UofGlasgow-ES-Team5/Centralized-Hazard-Detection-System-/Images/Schematic_Diagrams/KiCad Schematic Files/CentralNode.kicad_sch

## KiCad design Images/Schematic_Diagrams/KiCad Schematic Files/CentralNode.kicad_sch (2024-04-15)

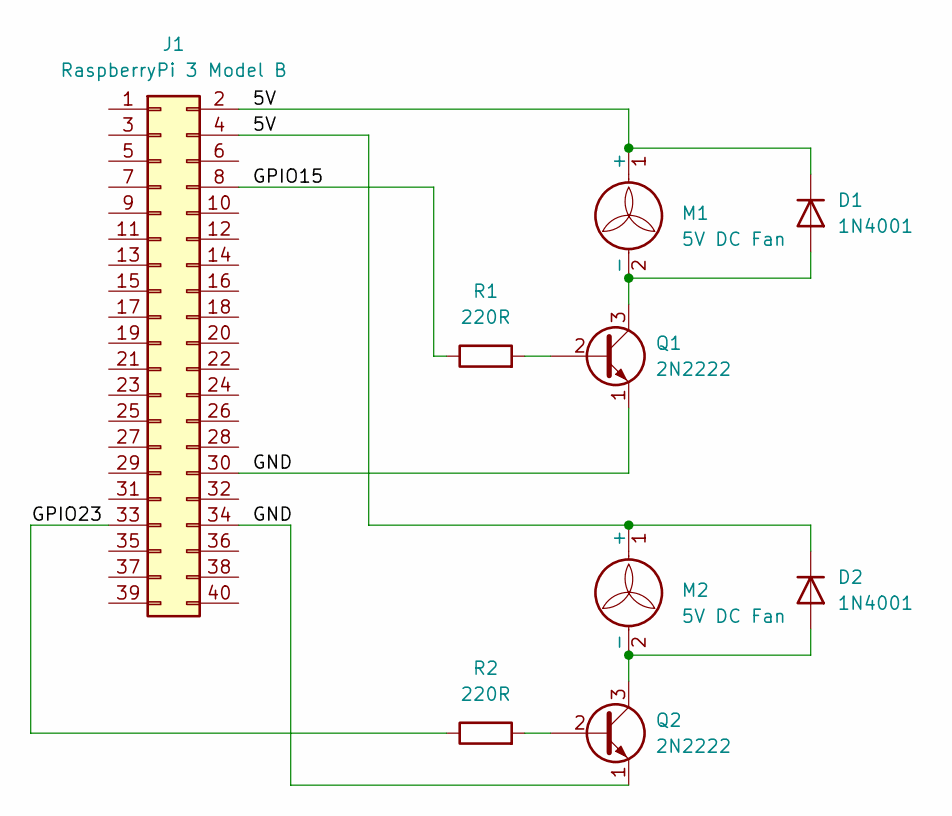
[picture p12: schematic CentralNode.kicad_sch]

Parts:
D1, D2: 1N4001; D_DO-247_Vertical
J1: RaspberryPi 3 Model B; PinHeader_2x20_P2.54mm_Vertical
M1, M2: 5V DC Fan
Q1, Q2: 2N2222; TO-39-3
R1, R2: 220R

Connections:
5V: D1.1 (K), D2.1 (K), J1.2, J1.4, M1.1 (+), M2.1 (+)
GND: J1.30, J1.34, Q1.1 (E), Q2.1 (E)
GPIO15: J1.8, R1.1
GPIO23: J1.33, R2.1
unnamed: D1.2 (A), M1.2 (-), Q1.3 (C)
unnamed: D2.2 (A), M2.2 (-), Q2.3 (C)
unnamed: Q1.2 (B), R1.2
unnamed: Q2.2 (B), R2.2
