UofGlasgow-ES-Team5/Centralized-Hazard-Detection-System-/Images/Schematic_Diagrams/KiCad Schematic Files/EdgeNode.kicad_sch

## KiCad design Images/Schematic_Diagrams/KiCad Schematic Files/EdgeNode.kicad_sch (2024-04-15)

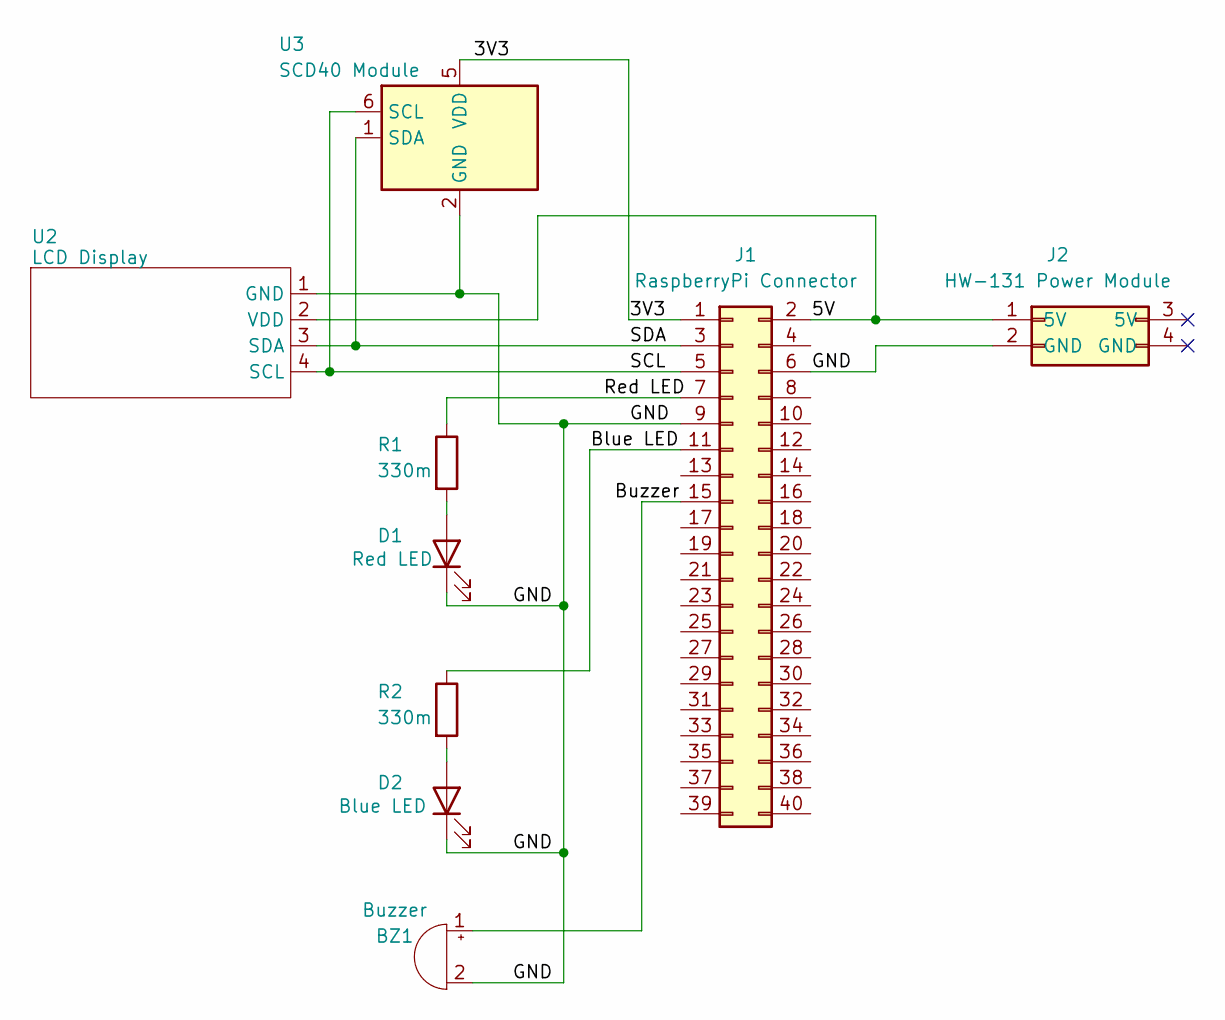
[picture p13: schematic EdgeNode.kicad_sch]

Parts:
BZ1: Buzzer
D1: Red LED
D2: Blue LED
J1: RaspberryPi Connector; PinHeader_2x20_P2.54mm_Vertical
J2: HW-131 Power Module
R1, R2: 330m
U2: LCD Display
U3: SCD40 Module; DFN-6-1EP_3x3mm_P1mm_EP1.65x2.55mm

Connections:
3V3: J1.1, U3.5 (VDD)
5V: J1.2, J2.1 (5V), U2.2 (VDD)
Blue LED: J1.11, R2.1
Buzzer: BZ1.1 (+), J1.15
GND: BZ1.2 (-), D1.1 (K), D2.1 (K), J1.6, J1.9, J2.2 (GND), U2.1 (GND), U3.2 (GND)
unnamed: D1.2 (A), R1.2
unnamed: D2.2 (A), R2.2
Red LED: J1.7, R1.1
SCL: J1.5, U2.4 (SCL), U3.6 (SCL)
SDA: J1.3, U2.3 (SDA), U3.1 (SDA)
