UofGlasgow-ES-Team5/Centralized-Hazard-Detection-System-/CentralNode/FileHandler.h

#ifndef FILEHANDLER_H
#define FILEHANDLER_H

#include <string>
#include "json.hpp"
#include "TCPServer.h"

class FileHandler {
public:
    static nlohmann::json readFileToJson();
    static void readFileAndRunServer(nlohmann::json& sensorLimits, TCPServer& server);
    static void writeToSensorDataFile(std::string sensorDataString, const nlohmann::json& sensorLimits);
    static void writeToLocationFile(int hazardZoneID);
};

#endif /* FILEHANDLER_H */
