UofGlasgow-ES-Team5/Centralized-Hazard-Detection-System-/EdgeNode/Client.h

#ifndef CLIENT_H
#define CLIENT_H

#include <iostream>
#include <cstring>
#include <cstdlib>
#include <unistd.h>
#include <arpa/inet.h>
#include <cstdio>
#include <regex>
#include <string>
#include <sys/socket.h>
#include <thread>
#include <chrono>
#include <atomic>

#include "json.hpp"

class Client {
private:
    std::string ip_address;
    const int PORT = 1350;
    std::atomic<bool> running{false};
    std::thread clientThread;
    std::string getRouterIP();
    void updateSensorLimits(nlohmann::json receivedJson, nlohmann::json &sensorDataLimits) ;

public:
    Client();
    void connectToServer(std::string &branchNodeIP, nlohmann::json &sensorData, nlohmann::json &sensorDataLimits);
};

#endif // CLIENT_H
