UofGlasgow-ES-Team5/Centralized-Hazard-Detection-System-/EdgeNode/WifiManager.h

#ifndef WIFIMANAGER_H
#define WIFIMANAGER_H

#include <iostream>
#include <fstream>
#include <sstream>
#include <vector>
#include <map>
#include <algorithm>
#include <regex>
#include <chrono>
#include <thread>

class WifiManager {
private:
    std::map<std::string, std::string> networkInfo;

    std::string findStrongestWifi(std::vector<std::pair<std::string, int>> &myMap);
    std::vector<std::pair<std::string, int>> scanForWifi();
    void connectToWifi(std::string SSID, std::string password);
    void connectToStrongestWifi(std::map<std::string, std::string> &networkInfo, std::string &closestWifi);

public:
    WifiManager();
    void startNetworkProcess(std::string &branchNode, std::string &branchNodeIP, std::map<std::string, std::string> &networkInfo);
    std::map<std::string, std::string> readNetworkFile();
};

#endif
